LuoouI/FOC_L/CYT/FOC_L/project/code/My_Key/My_Key.h

#ifndef MY_KEY_H_
#define MY_KEY_H_

#include "zf_common_headfile.h"

/*==================================================== 基础函数 ====================================================*/
void    My_Key_Service          (void);
/*==================================================== 基础函数 ====================================================*/

#endif
