LuoouI/FOC_L/CYT/FOC_L/project/user/cm4_isr.c

/*********************************************************************************************************************
* CYT2BL3 Opensourec Library 即（ CYT2BL3 开源库）是一个基于官方 SDK 接口的第三方开源库
* Copyright (c) 2022 SEEKFREE 逐飞科技
*
* 本文件是 CYT2BL3 开源库的一部分
*
* CYT2BL3 开源库 是免费软件
* 您可以根据自由软件基金会发布的 GPL（GNU General Public License，即 GNU通用公共许可证）的条款
* 即 GPL 的第3版（即 GPL3.0）或（您选择的）任何后来的版本，重新发布和/或修改它
*
* 本开源库的发布是希望它能发挥作用，但并未对其作任何的保证
* 甚至没有隐含的适销性或适合特定用途的保证
* 更多细节请参见 GPL
*
* 您应该在收到本开源库的同时收到一份 GPL 的副本
* 如果没有，请参阅<https://www.gnu.org/licenses/>
*
* 额外注明：
* 本开源库使用 GPL3.0 开源许可证协议 以上许可申明为译文版本
* 许可申明英文版在 libraries/doc 文件夹下的 GPL3_permission_statement.txt 文件中
* 许可证副本在 libraries 文件夹下 即该文件夹下的 LICENSE 文件
* 欢迎各位使用并传播本程序 但修改内容时必须保留逐飞科技的版权声明（即本声明）
*
* 文件名称          cm4_isr
* 公司名称          成都逐飞科技有限公司
* 版本信息          查看 libraries/doc 文件夹内 version 文件 版本说明
* 开发环境          IAR 9.40.1
* 适用平台          CYT2BL3
* 店铺链接          https://seekfree.taobao.com/
*
* 修改记录
* 日期              作者                备注
* 2024-1-9      pudding            first version
* 2024-5-14     pudding            新增12个pit周期中断 增加部分注释说明
********************************************************************************************************************/

#include "My_Headfile.h"

// **************************** PIT中断函数 ****************************
void pit0_ch0_isr()                     // 定时器通道 0 周期中断服务函数      
{
    pit_isr_flag_clear(PIT_CH0);
  
}

void pit0_ch1_isr()                     // 定时器通道 1 周期中断服务函数      
{
    pit_isr_flag_clear(PIT_CH1);
}

void pit0_ch2_isr()                     // 定时器通道 2 周期中断服务函数      
{
    pit_isr_flag_clear(PIT_CH2);

    /* 估算电机转矩 */
    Motor_Torque_Estimate();

    /* 更新上位机协议时间基准 */
    Foc_Protocol_Tick1ms();

}

void pit0_ch10_isr()                    // 定时器通道 10 周期中断服务函数      
{
    pit_isr_flag_clear(PIT_CH10);
    
   /* 勿动（计数器和adc冲突）*/
}

void pit0_ch11_isr()                    // 定时器通道 11 周期中断服务函数      
{
    pit_isr_flag_clear(PIT_CH11);
    
    /* 按键扫描  若要使用按键需要按键初始化 */
    // key_scanner();   

    /* LED服务函数 */
    My_LED_CheckVoltage();
    My_LED_Service(10u);

}

void pit0_ch12_isr()                    // 定时器通道 12 周期中断服务函数      
{
    pit_isr_flag_clear(PIT_CH12);
    
}

void pit0_ch13_isr()                    // 定时器通道 13 周期中断服务函数      
{
    pit_isr_flag_clear(PIT_CH13);
    
}

void pit0_ch14_isr()                    // 定时器通道 14 周期中断服务函数      
{
    pit_isr_flag_clear(PIT_CH14);
    
}

void pit0_ch15_isr()                    // 定时器通道 15 周期中断服务函数      
{
    pit_isr_flag_clear(PIT_CH15);
    
}

void pit0_ch16_isr()                    // 定时器通道 16 周期中断服务函数      
{
    pit_isr_flag_clear(PIT_CH16);
    
}

void pit0_ch17_isr()                    // 定时器通道 17 周期中断服务函数      
{
    pit_isr_flag_clear(PIT_CH17);
    
}

void pit0_ch18_isr()                    // 定时器通道 18 周期中断服务函数      
{
    pit_isr_flag_clear(PIT_CH18);
    
}

void pit0_ch19_isr()                    // 定时器通道 19 周期中断服务函数      
{
    pit_isr_flag_clear(PIT_CH19);
    
}

void pit0_ch20_isr()                    // 定时器通道 20 周期中断服务函数      
{
    pit_isr_flag_clear(PIT_CH20);
    
}

void pit0_ch21_isr()                    // 定时器通道 21 周期中断服务函数      
{
    pit_isr_flag_clear(PIT_CH21);
    
}
// **************************** PIT中断函数 ****************************


// **************************** 串口中断函数 ****************************
// 串口0默认作为调试串口
/***********************************************
 * @brief : 从串口0接收寄存器取出字节并交给FOC协议缓冲
 * @param : 无
 * @return: 无
 * @date  : 2026-09-28
 * @author: L
 ************************************************/
void uart0_isr (void)
{
    uint8 Receive_data;

    if (uart_isr_mask(UART_0) != 0u)
    {
        if (uart_query_byte(UART_0, &Receive_data) != 0u)
        {
            Foc_Protocol_ReceiveByte(Receive_data);
        }
    }
    else                                 // 串口0发送中断
    {           
        
        
        
    }
}

void uart1_isr (void)
{
    if(uart_isr_mask(UART_1))            // 串口1接收中断
    {
        
        
      
      
    }
    else                                // 串口1发送中断
    {
      
        
        
        
    }
}

void uart2_isr (void)
{
    if(uart_isr_mask(UART_2))            // 串口2接收中断
    {
        
      
        
        
    }
    else                                // 串口2发送中断
    {
        
        
        
       
    }
}

void uart3_isr (void)
{
    if(uart_isr_mask(UART_3))            // 串口3接收中断
    {
        

        
        
    }
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



}

void gpio_21_exti_isr()                  // 外部 GPIO_21 中断服务函数     
{



}

void gpio_22_exti_isr()                  // 外部 GPIO_22 中断服务函数     
{



}

void gpio_23_exti_isr()                  // 外部 GPIO_23 中断服务函数     
{



}
// **************************** 外部中断函数 ****************************
